dg1yfe/mcmega/menu_sub.c

/*
 * menu_sub.c
 *
 *  Created on: 17.06.2012
 *****************************************************************************
 *	MCmega - Firmware for the Motorola MC micro radio
 *           to use it as an Amateur-Radio transceiver
 *
 * Copyright (C) 2013 Felix Erckenbrecht, DG1YFE
 *
 * ( AVR port of "MC70"
 *   Copyright (C) 2004 - 2013  Felix Erckenbrecht, DG1YFE)
 *
 * This file is part of MCmega.
 *
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
 ****************************************************************************
 */
#include <stdint.h>
#include <stdlib.h>
#include <avr/pgmspace.h>
#include <avr/eeprom.h>
#include <stdio.h>
#include <string.h>

#include "FreeRTOS.h"
#include "task.h"

#include "macros.h"
#include "regmem.h"
#include "io.h"
#include "menu.h"
#include "display.h"
#include "eeprom.h"
#include "subs.h"
#include "audio.h"
#include "ui.h"

void m_ctcss_submenu(char key);

// Small Submenus
//
//
//
//
//
//*******************************
// M   P O W E R
//
// set high or low power via menu

// Power Umschaltung
//
// ---------
// ONLY EVA9
// ---------
//
//
void m_power()
{
	if(config.powerMode)
	{
		// pwr is low, set to high
		rfpwr_set(1);
	}
	else
	{
		// pwr is high, set to low
		rfpwr_set(0);
	}
	rfpwr_print();
}



void m_power_submenu(char key)
{
	char print = 0;

	m_reset_timer();

	if(m_state != POWER_SELECT)
	{
		m_state = POWER_SELECT;
		print = 1;
	}
	else
	{
		switch(key)
		{
			case KC_D1:
			case KC_D2:
				config.powerMode ^= 1;
				print = 1;
				break;
			case KC_ENTER:
// TODO: Revert to initial value on "exit"
			case KC_EXIT:
				m_timer = 0;
				break;
			default:
				break;
		}
	}

	if(print)
	{
		lcd_cpos(0);
		if(config.powerMode)
		{
			printf_P(PSTR("pwr lo"));
			arrow_set(3, 0);
		}
		else
		{
			printf_P(PSTR("pwr hi"));
			arrow_set(3, 1);
		}

		lcd_fill();
	}
}

//**************************************
//
//

void m_cfgsave_submenu(char key)
{
	static char index;
	char print = 1;

	m_reset_timer();

	if (m_state != CONFIG_SELECT)
	{
		index = config.configAutosave & CONFIG_SAVE_AUTO;
		m_state = CONFIG_SELECT;
	}
	else
	{
		switch(key)
		{
			case KC_D1:
			{
				index = index > 1 ? 0 : index+1;
				break;
			}
			case KC_D2:
			{
				index = index ? index-1 : 2;
				break;
			}
			case KC_ENTER:
			{
				print = 0;
				if(!(index & CONFIG_SAVE_NOW))
				{
					uint8_t buf;

					buf = (index & CONFIG_SAVE_AUTO);
					cfgUpdate.cfgdata = buf;
					cfgUpdate.updateMask = CONFIG_UM_CONFIGAUTOSAVE;
					config_sendUpdate();
					lcd_cpos(0);
					printf_P(m_ok_str);
					lcd_fill();
					vTaskDelay(500);
					m_timer = 0;
				}
				else
				{
					char err;
					// Store current frequency and shift to EEPROM as power-up default
					// TODO: Store config structure to EEPROM
					cfgUpdate.updateMask = CONFIG_UM_SAVE_TO_EEPROM;
					config_sendUpdate();
					
					lcd_cpos(0);
					printf_P(m_ok_str);
					lcd_fill();
					vTaskDelay(500);
					lcd_cpos(0);
					printf_P(m_stored_str);
					lcd_fill();
					vTaskDelay(1000);
					m_timer = 0;
				}
				break;
			}
			case KC_EXIT:
			{
				print = 0;
				m_timer = 0;
				break;
			}
		}
	}

	if(print)
	{
		lcd_cpos(0);
		switch(index)
		{
		case CONFIG_SAVE_MANUAL: // manual
			printf_P(PSTR("MANUAL"));
			break;
		case CONFIG_SAVE_AUTO: // automatic
			printf_P(PSTR("AUTO"));
			break;
		default: // store now
			printf_P(PSTR("STORE"));
			break;
		}
		lcd_fill();
	}

}


//**************************************
//
//
void m_version_submenu(char key)
{
	m_state=SHOW_VERSION;
	m_reset_timer();
	lcd_cpos(0);
	printf_P(version_str);
	lcd_fill();
	if(key == KC_EXIT)
		m_timer=0;
}



//**************************************
//
//
void m_ctcss_tx(char key)
{
	m_state = CTCSS_SEL_TX;
	m_ctcss_submenu(-1);
}


void m_ctcss_rx(char key)
{
	m_state = CTCSS_SEL_RX;
	m_ctcss_submenu(-1);
}


void m_ctcss_submenu(char key)
{
	char print = 1;
	uint8_t ctcss_index;
	uint8_t	ctcss_index_other;
	
	m_reset_timer();

	if(m_state == CTCSS_SEL_TX)
	{
		ctcss_index = config.ctcssIndexTx;
		ctcss_index_other = config.ctcssIndexRx;
	}	
	else
	{
		ctcss_index = config.ctcssIndexRx;
		ctcss_index_other = config.ctcssIndexTx;
	}	


	// avoid "same as RX" / "same as TX" for bith settings
	// if it happens (eg invalid config), force current index to "CTCSS off" position
	if(!ctcss_index && (ctcss_index == ctcss_index_other)){
		ctcss_index = 1;
	}

	if (key != -1)
	{
		switch(key)
		{
			case KC_D1:
			{
				ctcss_index = ctcss_index < CTCSS_TABMAX-1 ? ctcss_index+1 : 0;
				// "same as RX" / "same as TX" can only be selected for TX or RX
				// otherwise there will be a paradoxon and the whole universe will cease to exist ;)
				if(!ctcss_index && (ctcss_index == ctcss_index_other)){
					ctcss_index++;
				}
				break;
			}
			case KC_D2:
			{
				ctcss_index = ctcss_index ? ctcss_index-1 : CTCSS_TABMAX-1;
				// "same as RX" / "same as TX" can only be selected for TX or RX
				// otherwise there will be a paradoxon and the whole universe will cease to exist ;)
				if(!ctcss_index && (ctcss_index == ctcss_index_other)){
					ctcss_index=CTCSS_TABMAX-1;
				}
				break;
			}
			case KC_ENTER:
			{
				print = 0;

				if(m_state == CTCSS_SEL_TX)
				{
					uint16_t freq;

					if(ctcss_index){
						freq = pgm_read_word(&ctcss_tab[ctcss_index]);
					}
					else{
						freq = pgm_read_word(&ctcss_tab[ctcss_index_other]);
					}						
						
					if(freq)
					{						
						tone_start_pl(freq);
					}
					else
					{
						tone_stop_pl();
						tone_decoder_stop();
						lcd_cpos(0);
						printf_P(PSTR("TX CTCSS"));
						lcd_fill();
						lcd_cpos(0);
						vTaskDelay(100);
						printf_P(PSTR("OFF"));
						lcd_fill();
						vTaskDelay(100);
					}
				}
				else
				{
					// CTCSS_SEL_RX
					uint16_t freq;

					if(ctcss_index){
						freq = pgm_read_word(&ctcss_tab[ctcss_index]);
					}
					else{
						freq = pgm_read_word(&ctcss_tab[ctcss_index_other]);
					}
									
					if(freq)
					{
						tone_decoder_start_freq(freq);
					}
					else
					{
						tone_decoder_stop();
						lcd_cpos(0);
						printf_P(PSTR("RX CTCSS"));
						lcd_fill();
						lcd_cpos(0);
						vTaskDelay(100);
						printf_P(PSTR("OFF"));
						lcd_fill();
						vTaskDelay(100);
					}
				}

				lcd_cpos(0);
				printf_P(m_ok_str);
				lcd_fill();
				m_timer=0;
				break;
			}
			case 0:
			{
				tone_stop_pl();
				tone_decoder_stop();
				lcd_cpos(0);
				printf_P(PSTR("TONE OFF"));
				lcd_fill();
				vTaskDelay(200);
			}
			// no break
			case KC_EXIT:
			{
				print = 0;
				m_timer = 0;
				break;
			}
		}
	}

	if(m_state == CTCSS_SEL_TX)
	{
		config.ctcssIndexTx = ctcss_index;
	}	
	else
	{
		config.ctcssIndexRx = ctcss_index;
	}	
	
	if(print)
	{
		uint16_t freq;
		char c[6];

		memset(c,0,sizeof c);
		
		if(ctcss_index){
			freq = pgm_read_word(&ctcss_tab[ctcss_index]);
		}
		else{
			freq = pgm_read_word(&ctcss_tab[ctcss_index_other]);
		}						
		itoa(freq,c,10);
		lcd_cpos(0);
		if(ctcss_index && (freq==0))
		{
			printf_P(PSTR("OFF"));
		}
		else
		{	if (freq == 0)
			{
				c[0]=' ';
				c[1]='O';
				c[2]='F';
				c[3]='F';
			}
			else
			if (freq<1000)
			{
				c[3] = c[2];
				c[2] = '_';
			}
			else
			{
				c[4] = c[3];
				c[3] = '_';
			}
			if(ctcss_index)
			{
				printf_P(PSTR("%s Hz"),c);				
			}
			else{
				if(m_state == CTCSS_SEL_TX)
					printf_P(PSTR("=RX%s"),c);
				else
					printf_P(PSTR("=TX%s"),c);				
			}
		}		
		lcd_fill();
	}

}




void m_cal_submenu(char key)
{
	uint8_t cal;

	m_reset_timer();
	m_state=CAL;
	cal = OSCCAL;

	switch(key)
	{
		case KC_D1:
		{
			cal++;
			break;
		}
		case KC_D2:
		{
			cal--;
			break;
		}
		case KC_EXIT:
		{
			m_timer=0;
			break;
		}
	}
	OSCCAL = cal;
	lcd_cpos(0);
	pputchar('x',cal,0);
	lcd_fill();

}
