dg1yfe/mcmega/int.c

/*
 * int.c
 *
 *  Created on: 26.05.2012
 *****************************************************************************
 *	MCmega - Firmware for the Motorola MC micro radio
 *           to use it as an Amateur-Radio transceiver
 *
 * Copyright (C) 2013 Felix Erckenbrecht, DG1YFE
 *
 * ( AVR port of "MC70"
 *   Copyright (C) 2004 - 2013  Felix Erckenbrecht, DG1YFE)
 *
 * This file is part of MCmega.
 *
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
 ****************************************************************************
 */
#include <avr/io.h>
#include <avr/interrupt.h>
#include <util/delay.h>

#include "FreeRTOS.h"
#include "task.h"

#include "regmem.h"
#include "io.h"
#include "audio.h"

volatile uint8_t int_wd_reset;
volatile uint8_t int_lcd_timer_dec;
volatile uint16_t PL_phase_delta;
volatile uint16_t SEL_phase_delta;
volatile uint16_t SEL_phase_delta2;
volatile unsigned int PL_phase;
volatile unsigned int SEL_phase;
volatile unsigned int SEL_phase2;


void vApplicationTickHook()
{

	tick_ms++;
	if(tick_ms == next_hms)
	{
		tick_hms++;
		next_hms+=100;
	}

	if(lcd_timer && int_lcd_timer_dec)
	{
		lcd_timer--;
	}

	gp_timer--;

}

// 8 kHz Interrupt for audio processing
// in RX: Get audio samples from ADC and store in sample buffer
// in TX: Run digital oscillators to produce signaling tones (CTCSS/DTMF/etc.)
ISR(TIMER2_COMP_vect)
{
	uint8_t index;
	static uint8_t samp_buf_w=0;
	static uint16_t dither = 1;

	if(!rxtx_state)	// process sample input in RX
	{
		if(tone_detector_active)
		{
			uint8_t sc;
/*
			uint32_t sb;
			sb=samp_buf;
			sb <<= 1;
			if(PIN_SIGIN & BIT_SIGIN)
			{
				sb |= 1;
			}
			samp_buf = sb;
*/
			// read latest sample from ADC
			samp_buf[samp_buf_w++] = ADCH;
			ADCSRA |= (1 << ADSC);		// start next conversion now
			samp_buf_w &= SAMP_BUF_LEN -1;
			sc = samp_buf_count;
			sc++;
			samp_buf_count = sc;
		}
	}
	else	// Tone oscillators are only used in TX
	{
		uint16_t pd;
		
		// check if CTCSS (Motorola speak 'private line') generator is active
		pd = PL_phase_delta;
		if(pd)
		{
			uint16_t ph;
			ph = PL_phase;
			ph += pd;
			PL_phase = ph;
			index = ph >> 8;
			index = pgm_read_byte(&sin_tab[index]);
			index >>=1;
			index |= PORT_PL_DAC & (~MASK_PL_DAC);
			PORT_PL_DAC = index;
		}

		// check if signaling generator is active with dual-tone
		pd=SEL_phase_delta2;
		if(pd)
		{
			uint8_t index2;
			uint16_t ph;
			
			ph = SEL_phase2;
			ph += pd;
			SEL_phase2 = ph;
			index2 = ph >> 8;
			index2 = pgm_read_byte(&sin_tab[index2]);

			ph = SEL_phase;
			ph += SEL_phase_delta;
			SEL_phase = ph;
			index = ph >> 8;
			index = pgm_read_byte(&sin_tab[index]);

			index+= index2;
			index >>= 1;
			index |= PORT_SEL_DAC & (~MASK_SEL_DAC);
			PORT_SEL_DAC = index;
		}
		else
		// check for single tone activity
		if( (pd=SEL_phase_delta) )
		{	uint16_t sp;
			uint8_t amplitude;
			sp = SEL_phase;
			sp += pd;
			SEL_phase = sp;
			index = sp >> 8;
			amplitude = pgm_read_byte(&rec_tab[index]);
			//amplitude -= 1;
			dither = (dither >> 1) ^ (-(dither & 1u) & 0xB400u);
			// add dithering
			//amplitude += ((uint8_t)dither) & 0x1;
			/*
			if(amplitude & 0x80){
				amplitude = 0;
			}
			else
			if(amplitude & 0x10){
				amplitude = 15;	
			}
			*/			
//			amplitude |= PORT_SEL_DAC & (uint8_t)(~MASK_SEL_DAC);
			PORT_SEL_DAC = amplitude;
		}
	}
}



void init_OCI()
{
	tick_ms = 0;
	tick_hms = 0;
	int_lcd_timer_dec = 0;
}

/*
 * Timer for DDS oscillator
 * runs at 8 kHz
 */
void init_Timer2()
{
#if (F_CPU / FS / 8) > 255
#warning "OCR2 value exceeds 255 - (OCR2 is the result of F_CPU / FS / 8 )"
#endif
	// when calculating the compare value, round to nearest integer (+4/8)
	OCR2 = (uint8_t) ( (F_CPU/FS + 4) / 8) - 1;
	TCCR2 |= (1 << WGM21) | (0 << WGM20) ;
	TIMSK |= (1 << OCIE2);
}


void start_Timer2()
{
	TCCR2 |= ((0 << CS22) | (1 << CS21) | (0 << CS20));
}


void stop_Timer2()
{
	if(!(SEL_phase_delta || PL_phase_delta || tone_detector_active))
	{
		TCCR2 &= ~((1 << CS22) | (1 << CS21) | (1 << CS20));
	}
}


// TODO: Analog Comparator ISR / Brown-Out detection
